osresearch/charliewatch/firmware/rtc.h

/*! \file rtc.h
  \brief Real Time Clock library.
*/

//! Flash buffer containing the manufacturing time.
extern const unsigned char romsavetime[];

//! Configure the Real Time Clock
void rtc_init();

//! Sets the DOW from the calendar date.
void rtc_setdow();

#include "rtcasm.h"
